zanny/rallycontroller/3D files - Roadbook IMO Handelbar control V1 - 4370615/images/20200517_053155.jpg

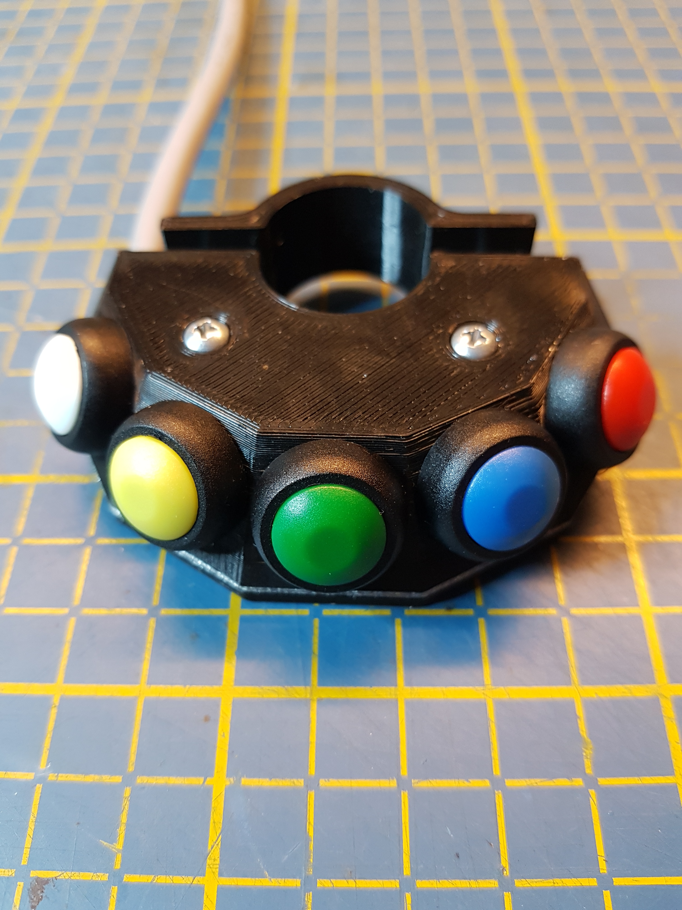
3D files - Roadbook IMO Handelbar control V1 - 4370615/images/20200517_053155.jpg
